tomtebloss/Atari_SF354_adapter/images/pcb top.jpg

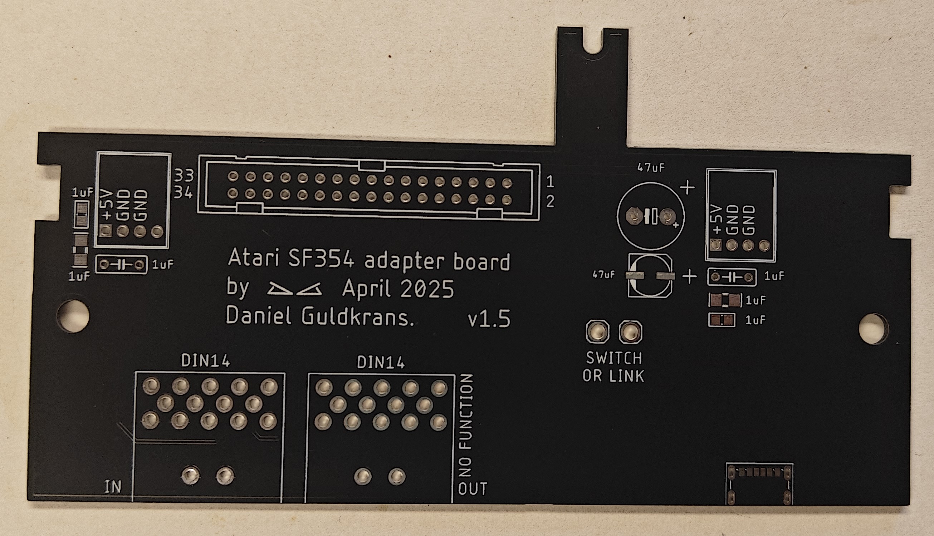
images/pcb top.jpg
